SantaClawzzz/TaltechHeat/Electronics/Outputs/Layout.jpg

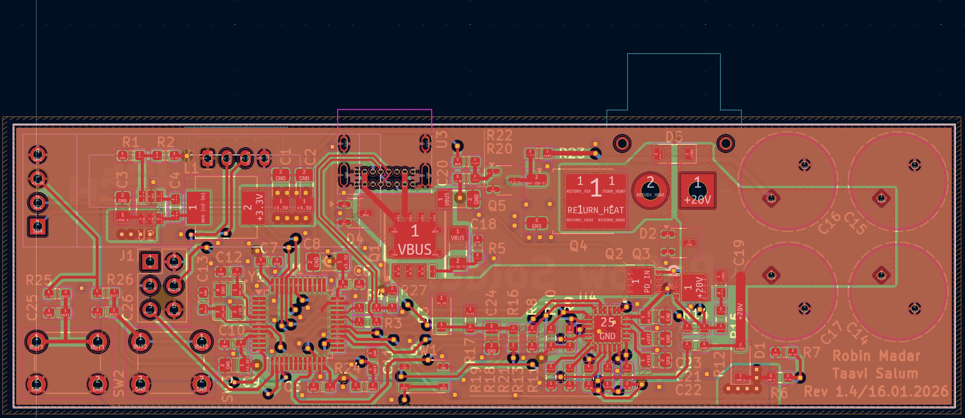
Electronics/Outputs/Layout.jpg
