SantaClawzzz/TaltechHeat/Electronics/Outputs/3D.jpg

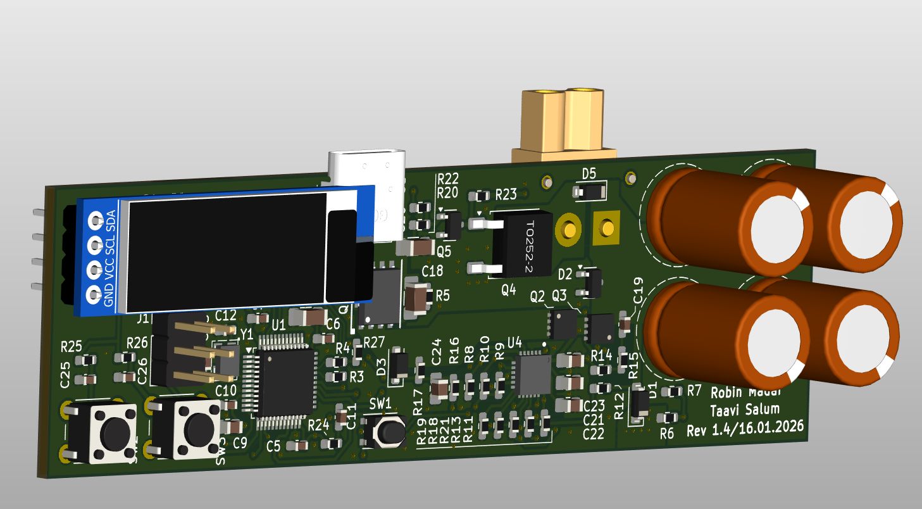
Electronics/Outputs/3D.jpg
