SantaClawzzz/TaltechHeat/Electronics/Outputs/DesignRules.jpg

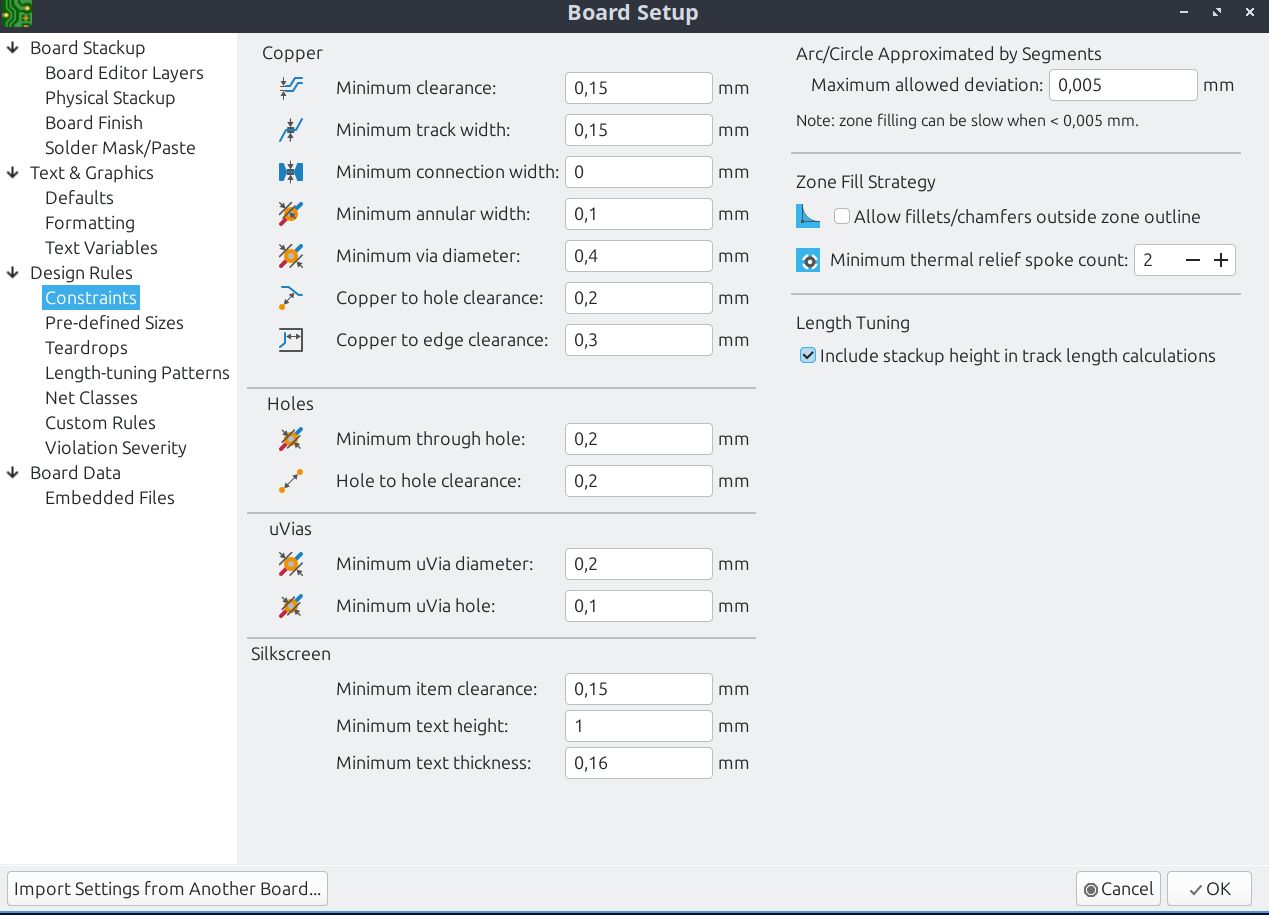
Electronics/Outputs/DesignRules.jpg
